mercenaruss/zigstar_gateways/documentation/docs/assets/images/radio-docs/Resistor-Swap.jpg

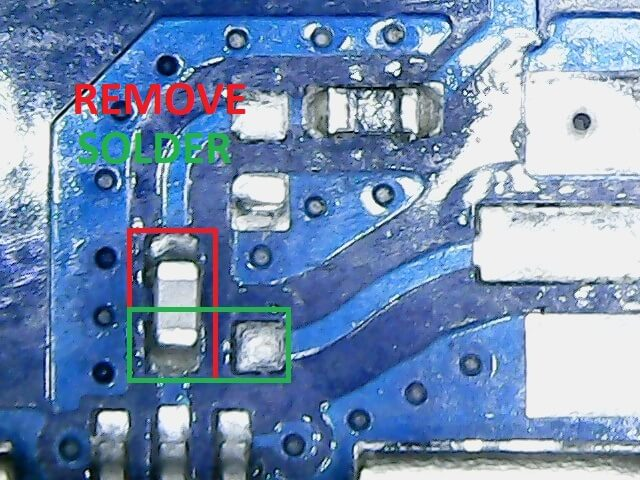
documentation/docs/assets/images/radio-docs/Resistor-Swap.jpg
