mercenaruss/zigstar_gateways/documentation/docs/assets/images/radio-docs/shield-bsl.png

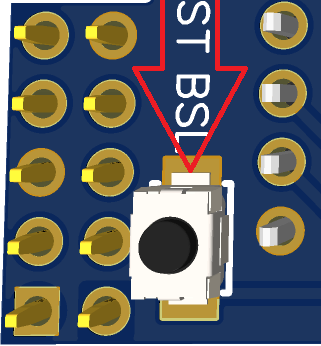
documentation/docs/assets/images/radio-docs/shield-bsl.png
