mercenaruss/zigstar_gateways/documentation/docs/assets/images/zigbee-gw-lan/ZSL - Sample.png

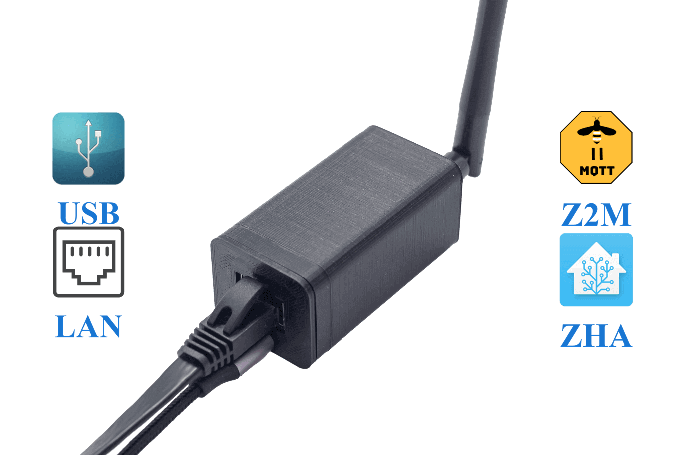
documentation/docs/assets/images/zigbee-gw-lan/ZSL - Sample.png
