mercenaruss/zigstar_gateways/documentation/docs/assets/images/zigbee-olizig/Olimex POE - 3.png

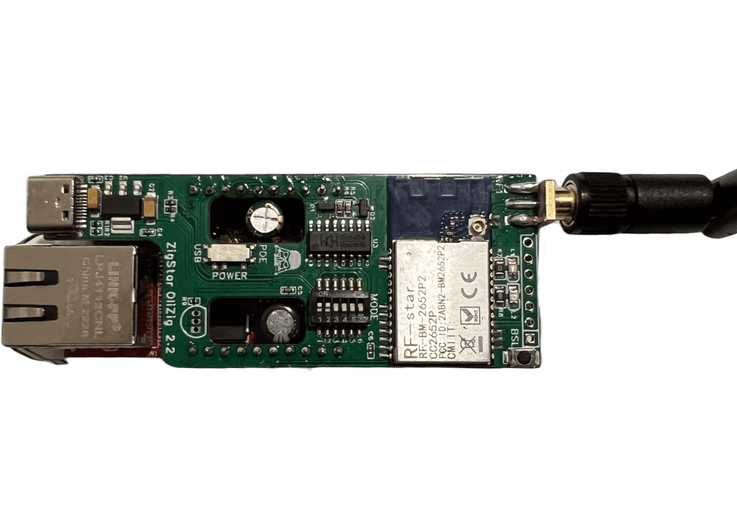
documentation/docs/assets/images/zigbee-olizig/Olimex POE - 3.png
