mercenaruss/zigstar_gateways/documentation/docs/assets/images/zigbee-zigihat/ZigiHAT-3.png

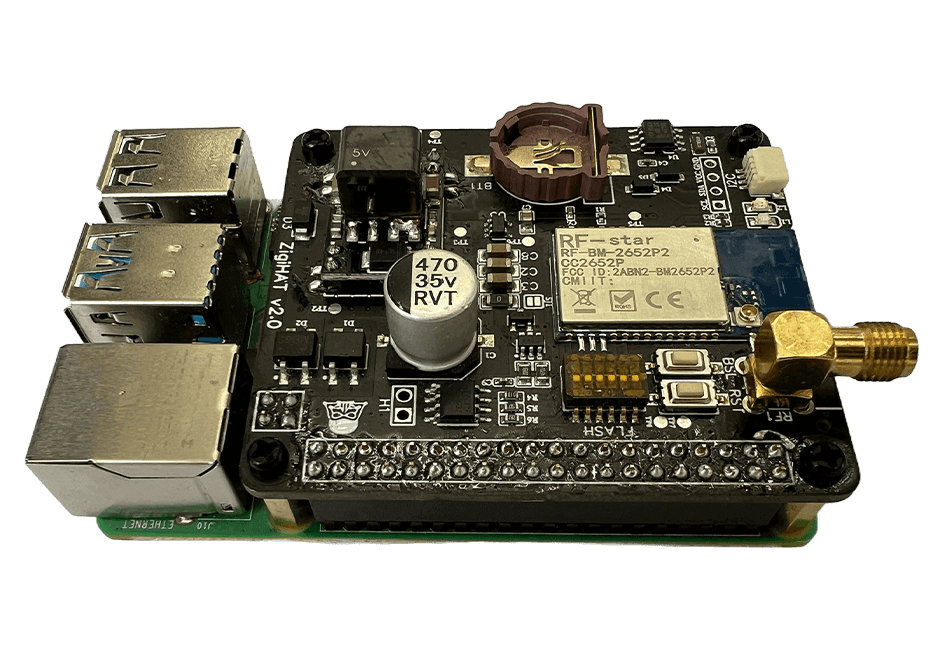
documentation/docs/assets/images/zigbee-zigihat/ZigiHAT-3.png
