mercenaruss/zigstar_gateways/documentation/docs/assets/images/zigstar-black.png

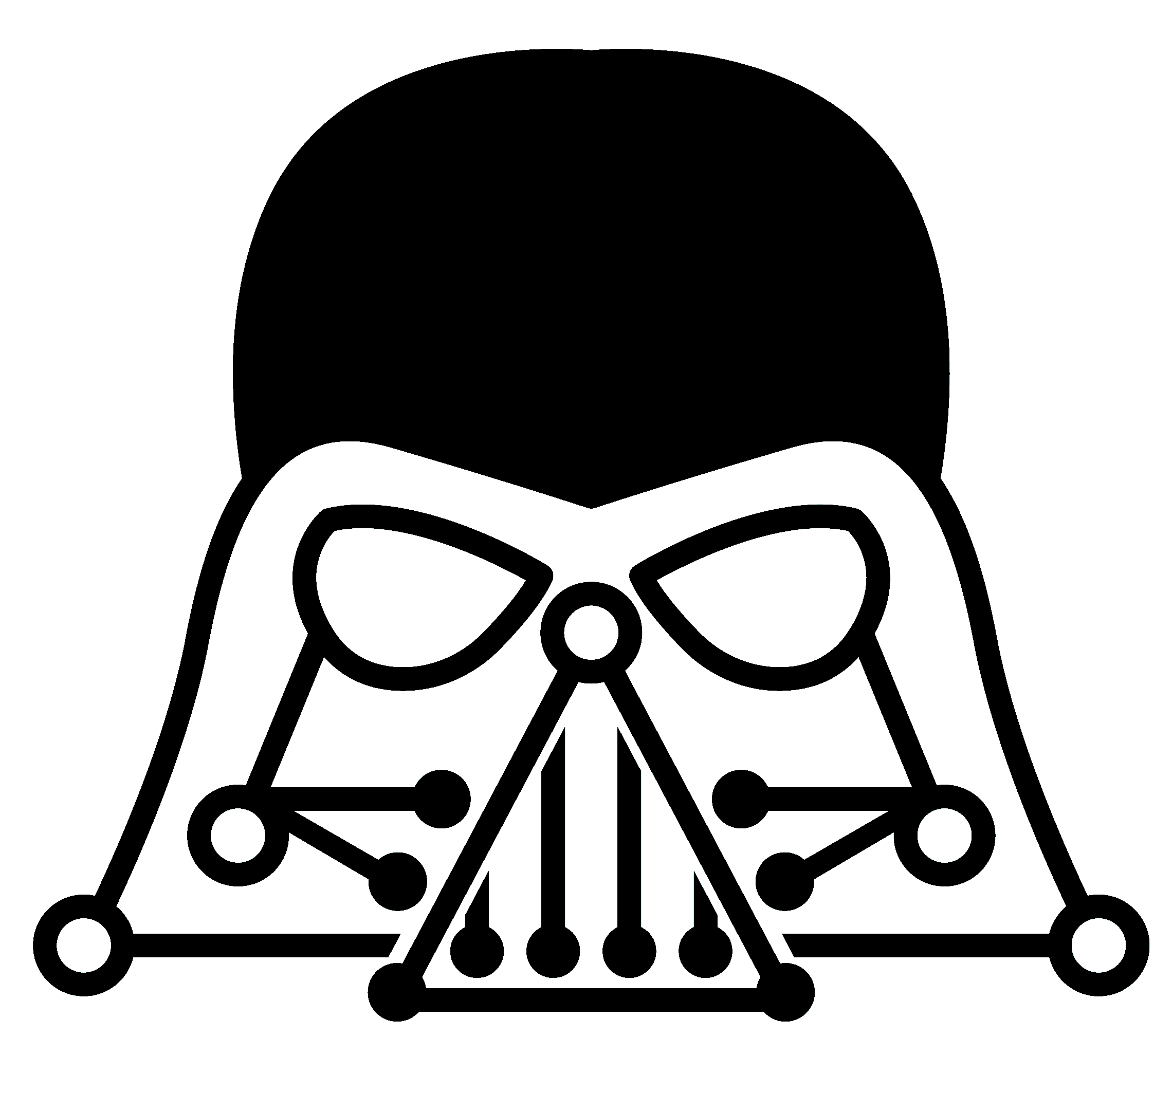
documentation/docs/assets/images/zigstar-black.png
