mercenaruss/zigstar_gateways/documentation/docs/assets/images/zigstar-white.png

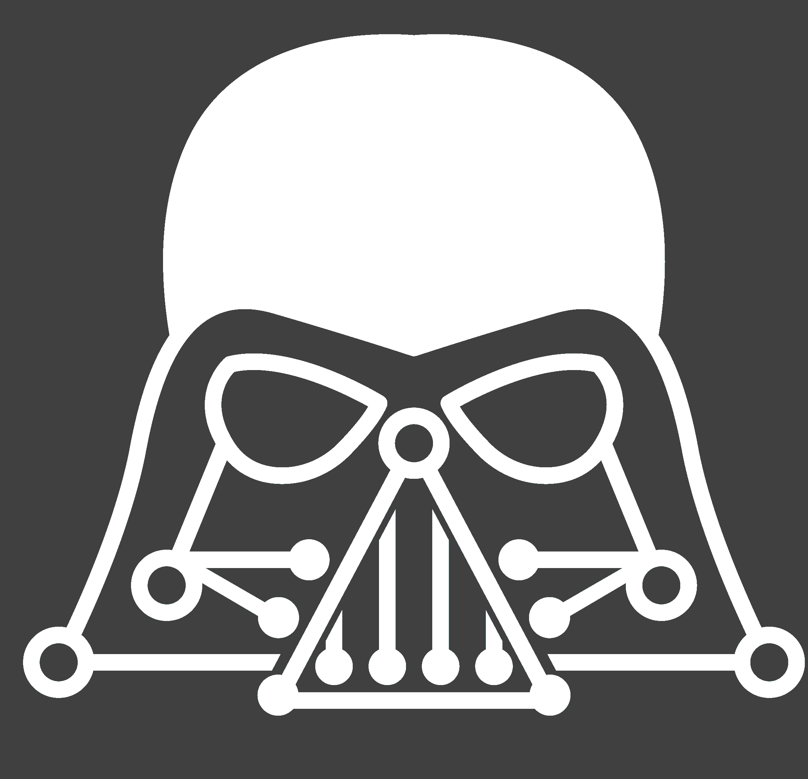
documentation/docs/assets/images/zigstar-white.png
