mercenaruss/zigstar_gateways/documentation/docs/assets/images/zigstar.png

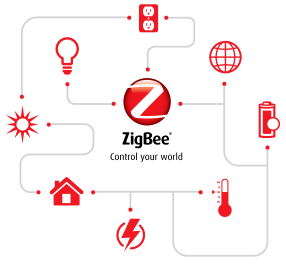
documentation/docs/assets/images/zigstar.png
